WhoTheHeck/ESP8266-Multisensor/images/IMG_1101.JPG

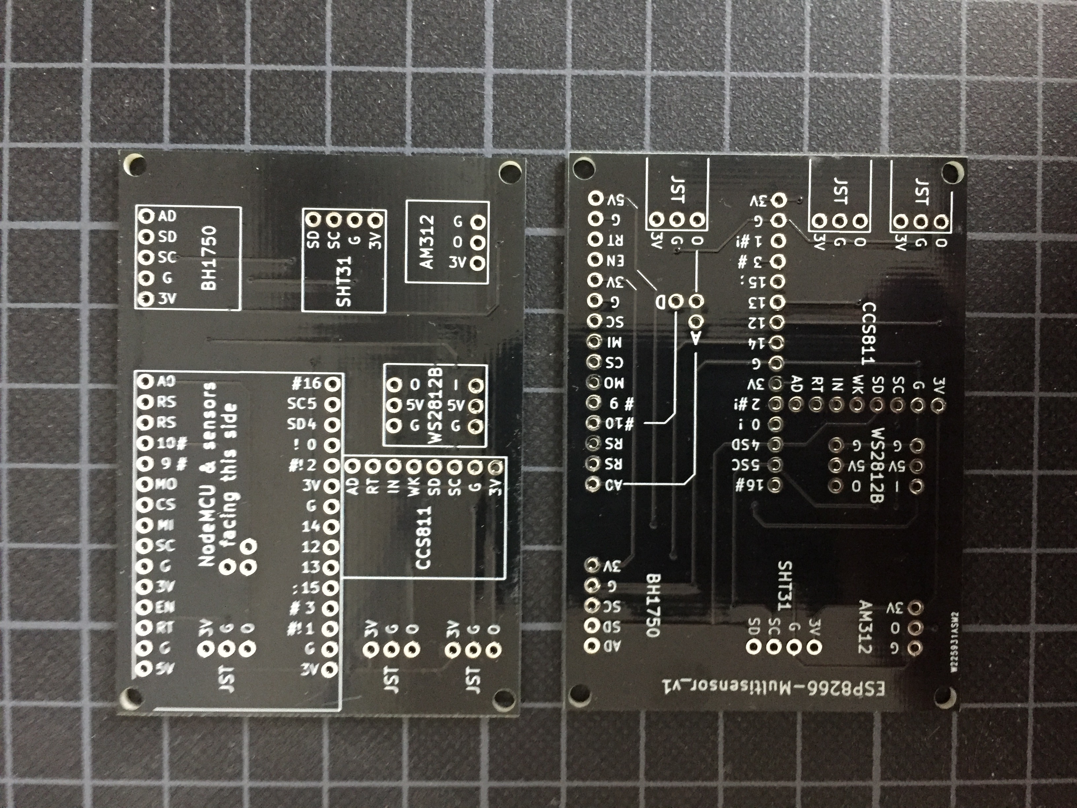
images/IMG_1101.JPG
