WhoTheHeck/ESP8266-Multisensor/images/IMG_1108.JPG

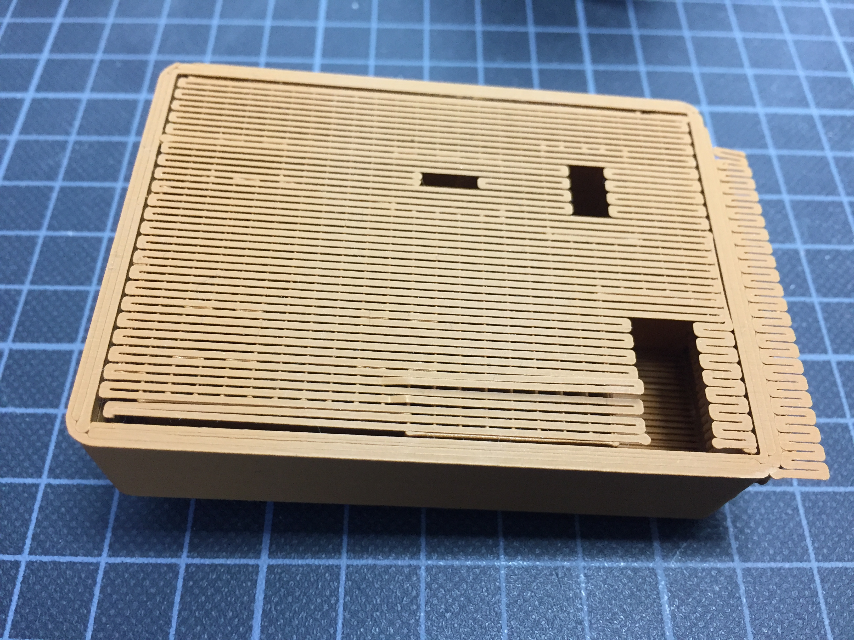
images/IMG_1108.JPG
