WhoTheHeck/ESP8266-Multisensor/images/IMG_1109.JPG

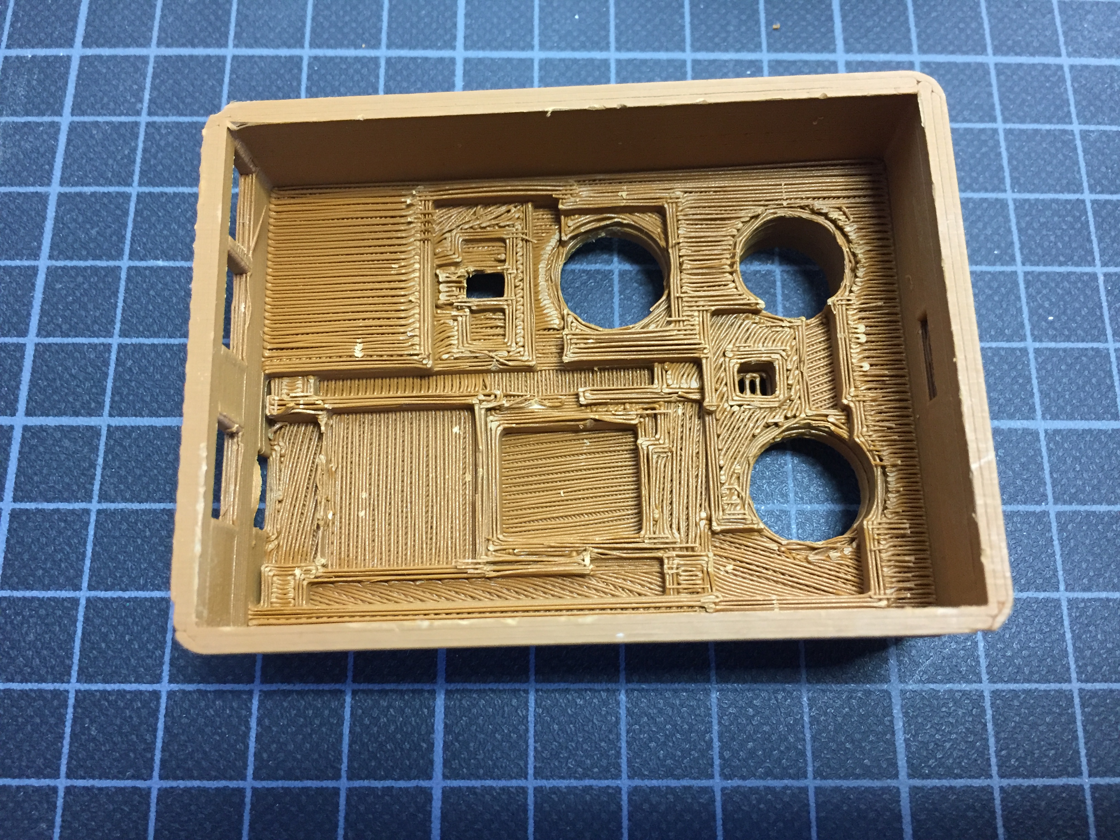
images/IMG_1109.JPG
